abhijay-py/secure-usb-drive/Software/STM32H7 Cube IDE/Core/Inc/lcd.h

/*
 * lcd.h
 *
 *  Created on: Feb 12, 2025
 *      Author: brand
 */

#ifndef INC_LCD_H_
#define INC_LCD_H_

#include "stm32h7xx_hal_spi.h"

#define HOME 0x46

void lcd_print(SPI_HandleTypeDef *hspi2, const uint8_t *string);
void lcd_welcome(SPI_HandleTypeDef *hspi2);
void lcd_clear(SPI_HandleTypeDef *hspi2);
void lcd_on(SPI_HandleTypeDef *hspi2);
void lcd_off(SPI_HandleTypeDef *hspi2);
void lcd_cursor_on(SPI_HandleTypeDef *hspi2);
void lcd_light(SPI_HandleTypeDef *hspi2, uint8_t brightness);
void lcd_display_first_row(SPI_HandleTypeDef *hspi2, uint8_t *string);
void lcd_display_second_row(SPI_HandleTypeDef *hspi2, uint8_t *string);
void lcd_cursor_location(SPI_HandleTypeDef *hspi2, const uint8_t hex_location);
void lcd_clear_cs(SPI_HandleTypeDef *hspi2);

void send_bytes(SPI_HandleTypeDef *hspi2, const uint8_t *tx_buffer, size_t size);

void periodic_send(SPI_HandleTypeDef *hspi2);

#endif /* INC_LCD_H_ */
